patriciacraciun/TSC-EBookReader/Images/Screenshot 2025-04-14 140654.png

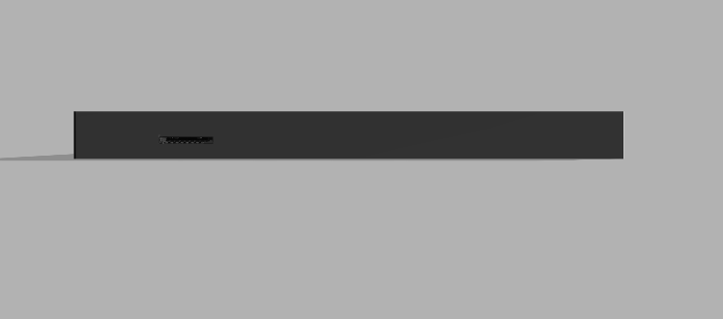
Images/Screenshot 2025-04-14 140654.png
