patriciacraciun/TSC-EBookReader/Images/Screenshot 2025-04-14 140704.png

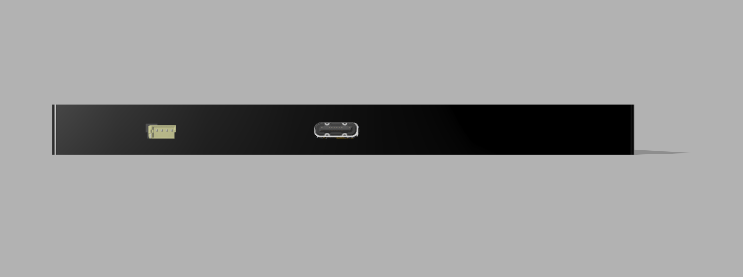
Images/Screenshot 2025-04-14 140704.png
