patriciacraciun/TSC-EBookReader/Images/Screenshot 2025-04-14 140846.png

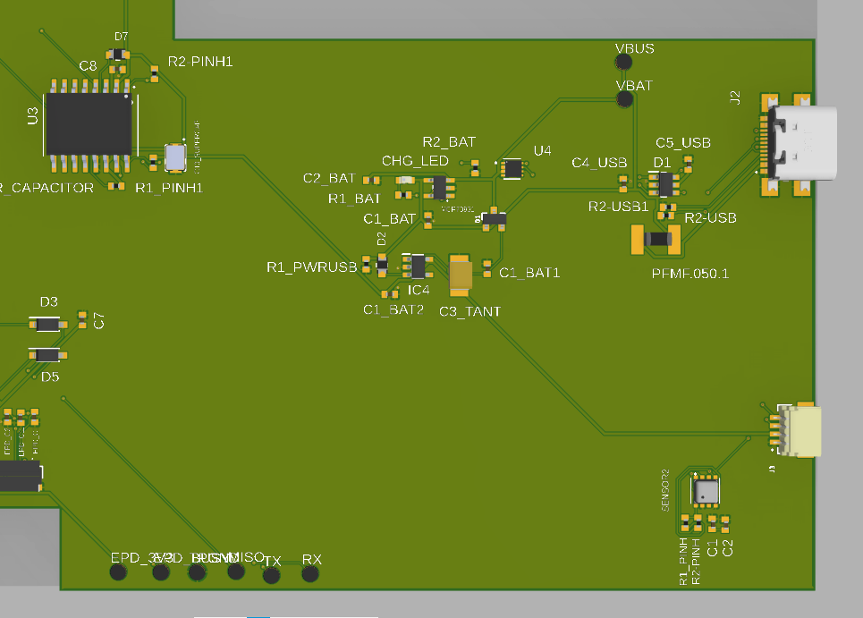
Images/Screenshot 2025-04-14 140846.png
