patriciacraciun/TSC-EBookReader/Images/Screenshot 2025-04-14 141532.png

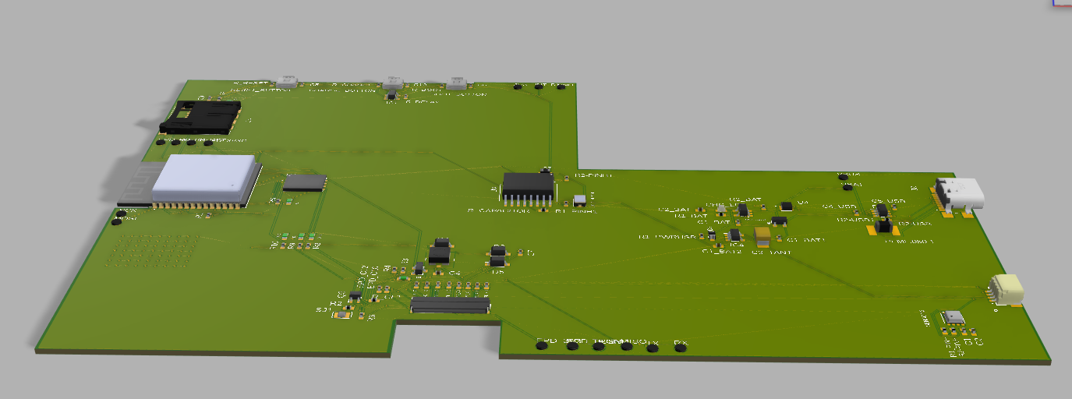
Images/Screenshot 2025-04-14 141532.png
