patriciacraciun/TSC-EBookReader/Images/Untitled_2025-Apr-12_01-21-24AM-000_CustomizedView12920613723.png

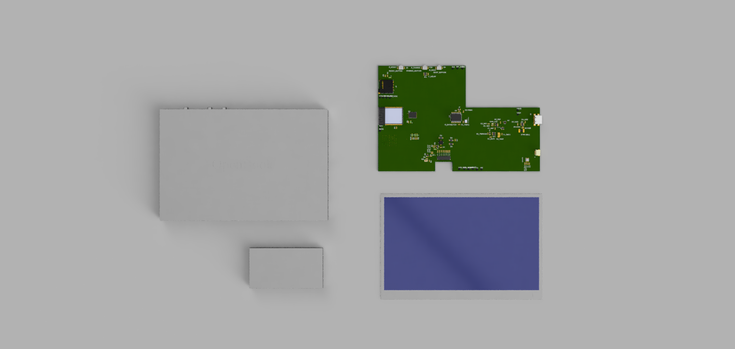
Images/Untitled_2025-Apr-12_01-21-24AM-000_CustomizedView12920613723.png
